curtstutsman/wireless_spotify_remote-display/final_esp32_code/JPEGDecoder/examples/Adafruit_GFX/Huzzah_Jpeg/data/EagleEye.jpg

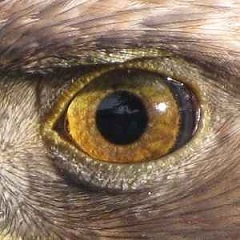
final_esp32_code/JPEGDecoder/examples/Adafruit_GFX/Huzzah_Jpeg/data/EagleEye.jpg
