curtstutsman/wireless_spotify_remote-display/final_esp32_code/JPEGDecoder/examples/Other libraries/SPIFFS_Jpeg/Data/tiger.jpg

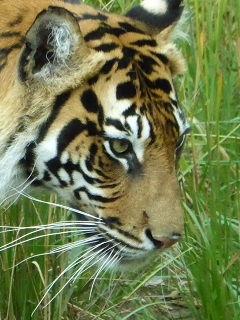
final_esp32_code/JPEGDecoder/examples/Other libraries/SPIFFS_Jpeg/Data/tiger.jpg
