curtstutsman/wireless_spotify_remote-display/final_esp32_code/JPEGDecoder/extras/arduino.jpg

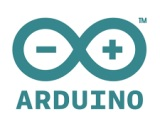
final_esp32_code/JPEGDecoder/extras/arduino.jpg
